dltech/usb_device3/datasheet/phone/Снимок экрана_2018-12-25_07-47-18.png

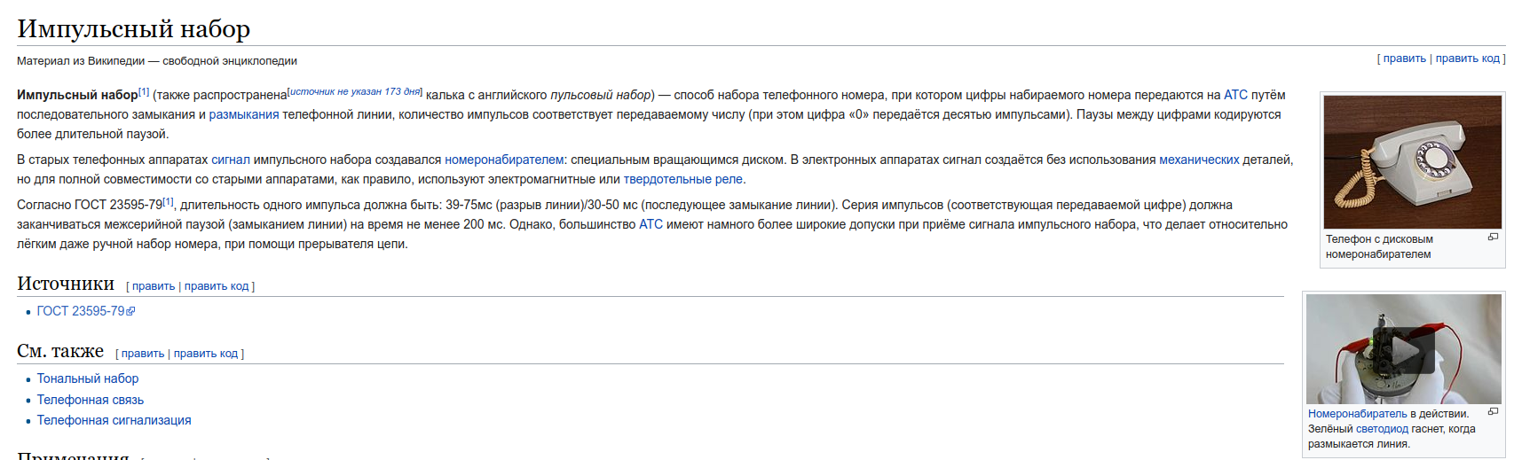
datasheet/phone/Снимок экрана_2018-12-25_07-47-18.png
