dltech/usb_device3/datasheet/webcam/images.jpeg

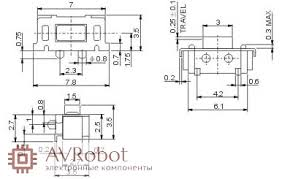
datasheet/webcam/images.jpeg
