dltech/usb_device3/doc/pic/Снимок экрана_2021-09-13_03-58-06.png

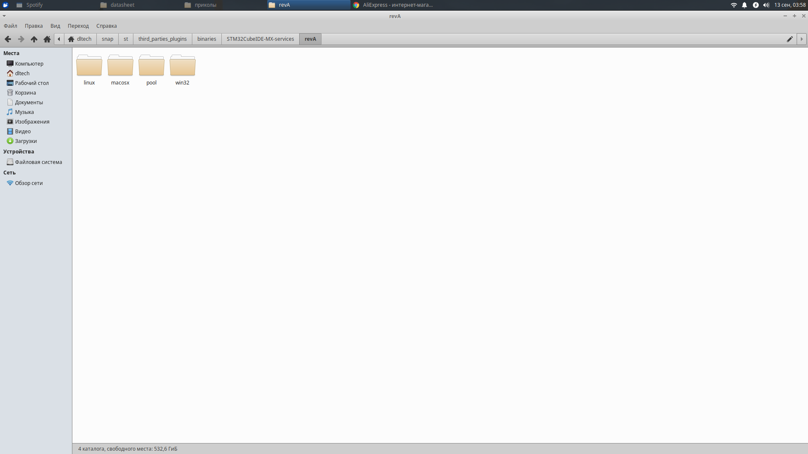
doc/pic/Снимок экрана_2021-09-13_03-58-06.png
