dltech/usb_device3/vid/hqdefault.jpg

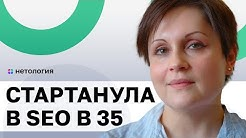
vid/hqdefault.jpg
