dltech/usb_device3/vid/red.png

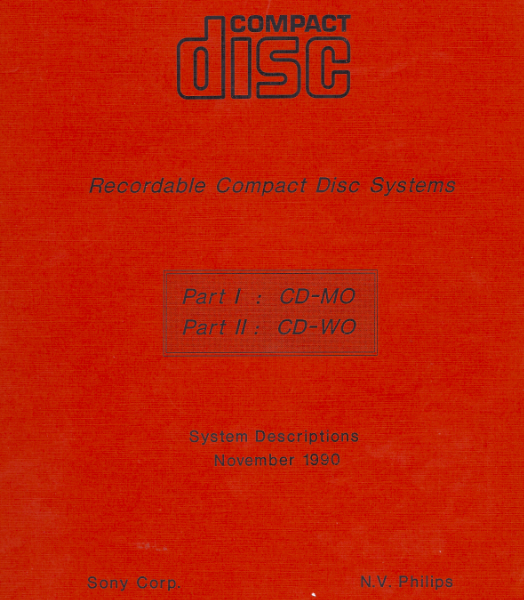
vid/red.png
