dltech/usb_device3/vid/usb_electrical.png

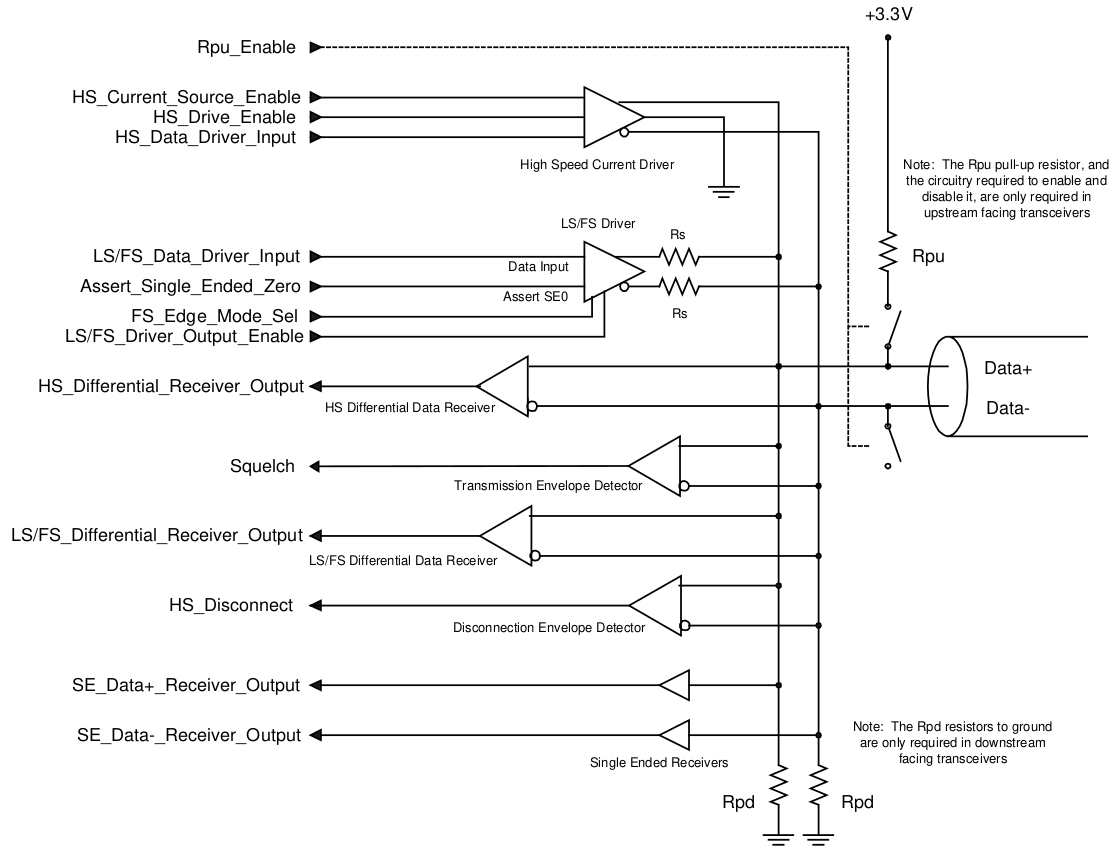
vid/usb_electrical.png
