dltech/usb_device3/vid/Кац_гриб.jpg

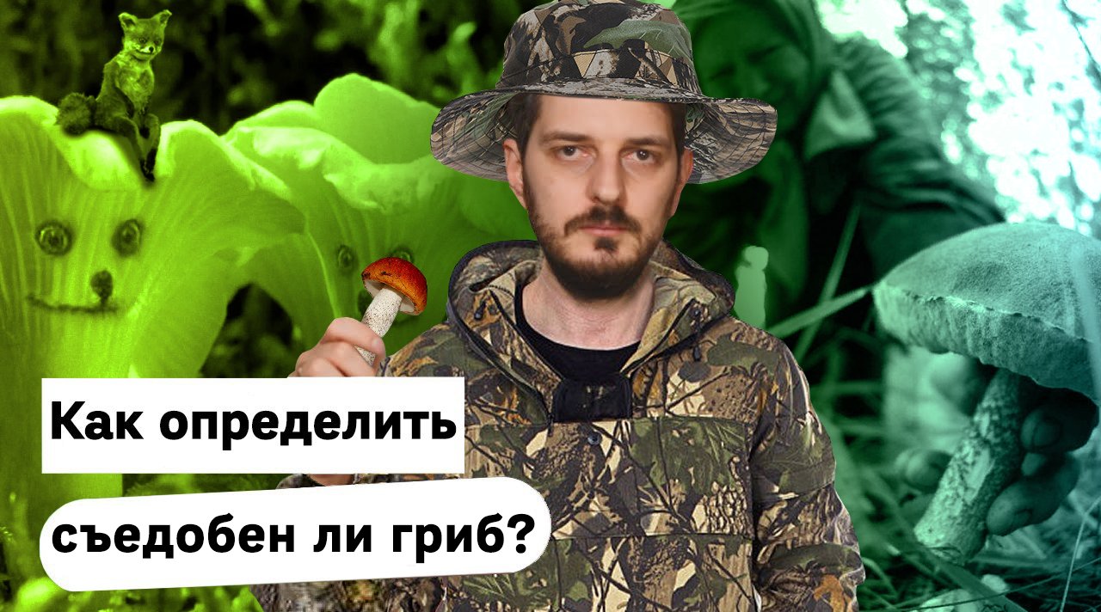
vid/Кац_гриб.jpg
