dltech/usb_device3/result/ambilight.png

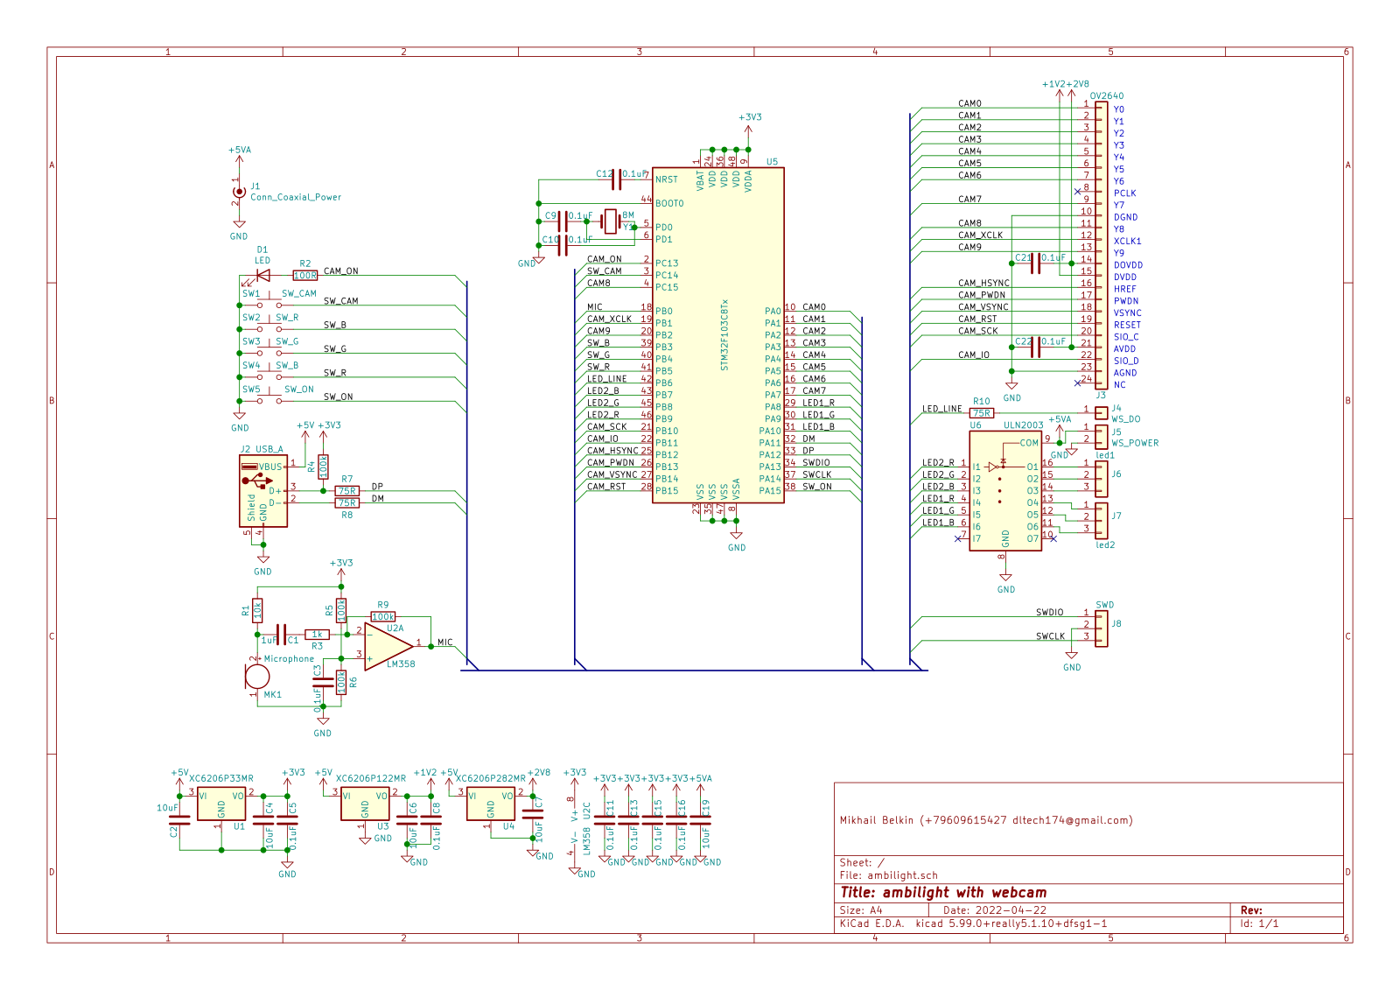
result/ambilight.png
