dltech/usb_device3/result/phone.png

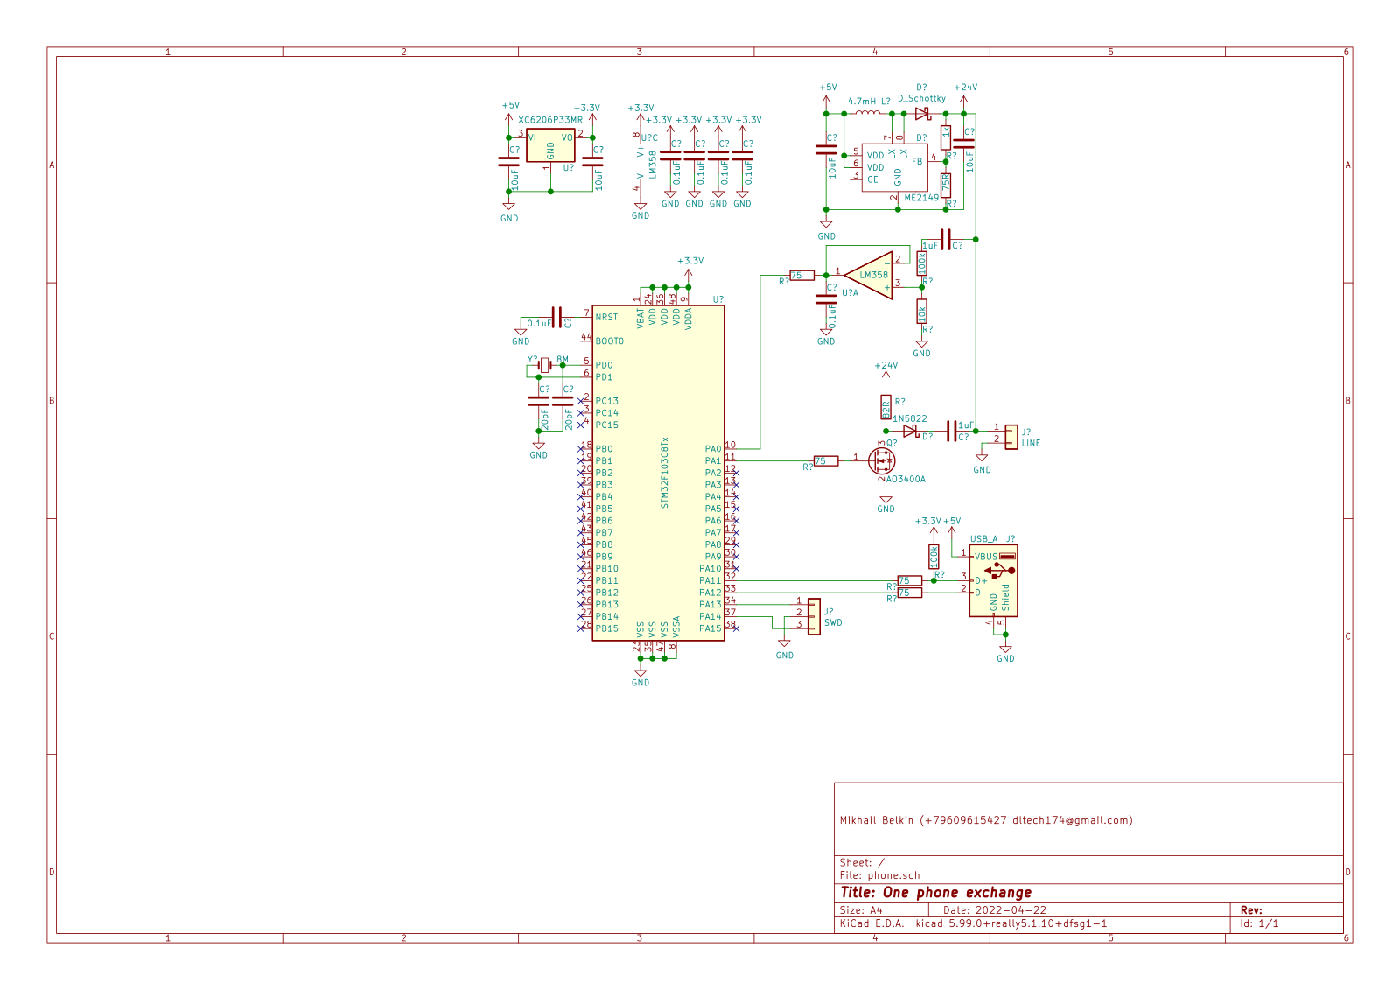
result/phone.png
