dltech/usb_device3/result/remote.png

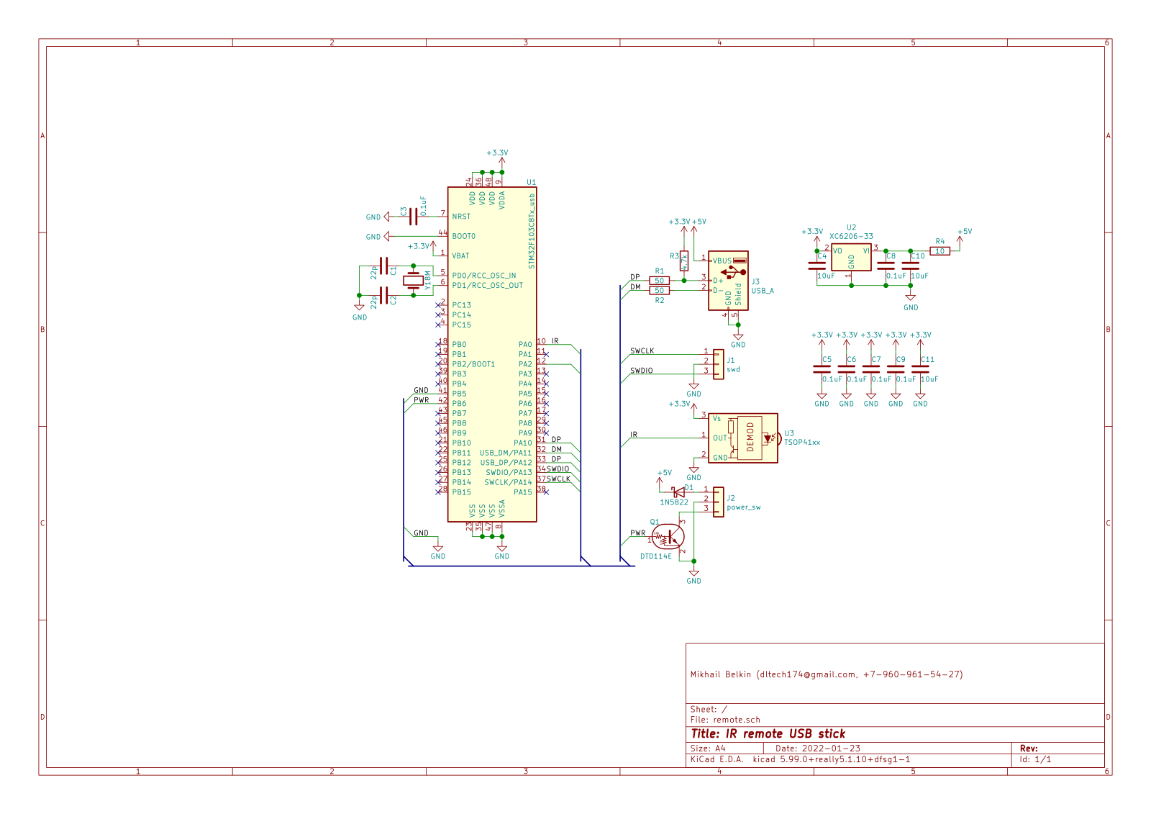
result/remote.png
