dltech/usb_device3/result/sch.png

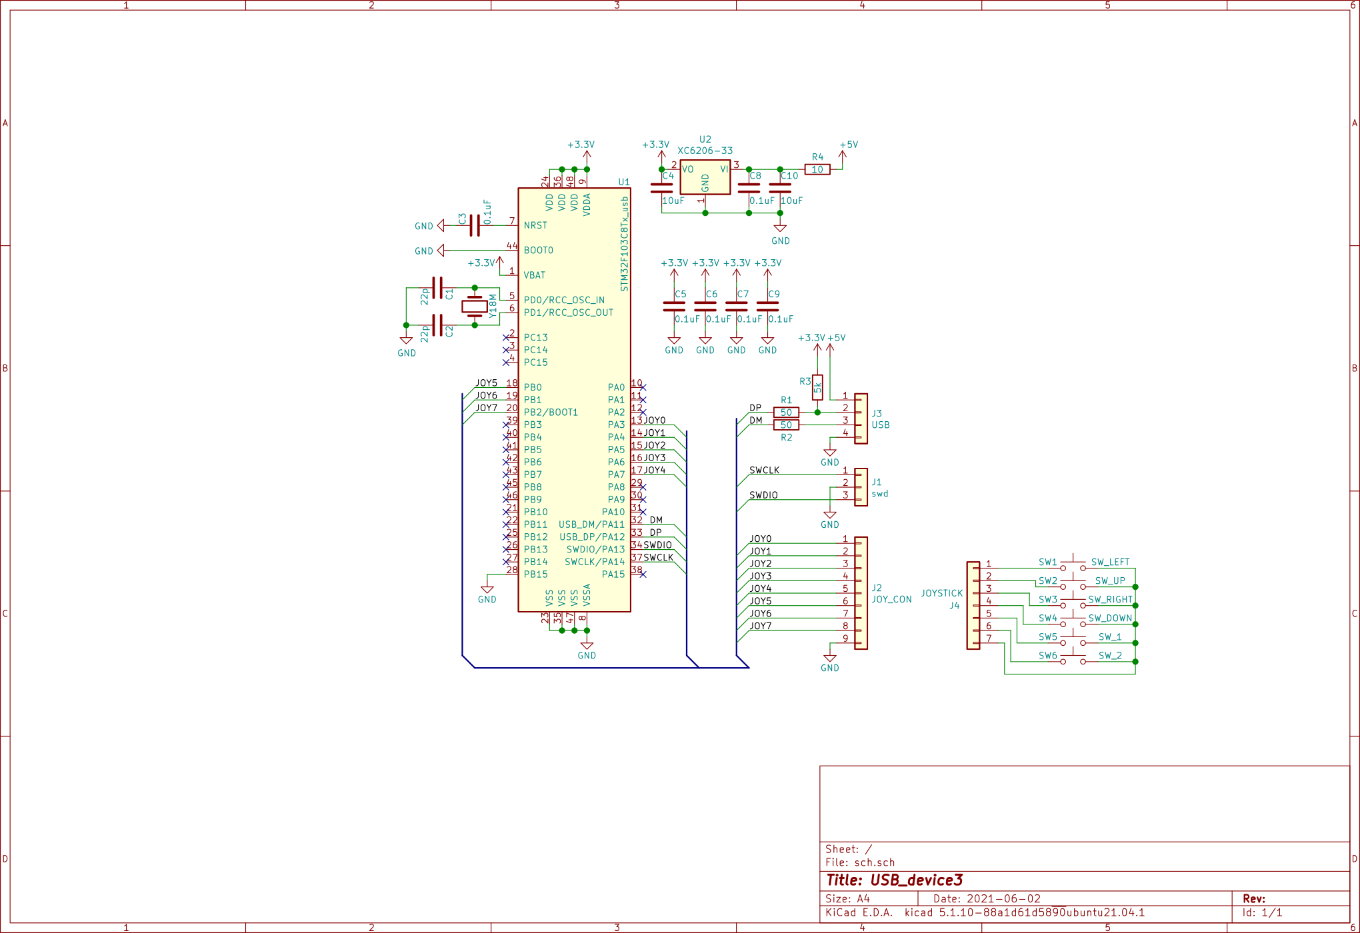
result/sch.png
